jazwa/rackstack/media/features/slideOpt.gif

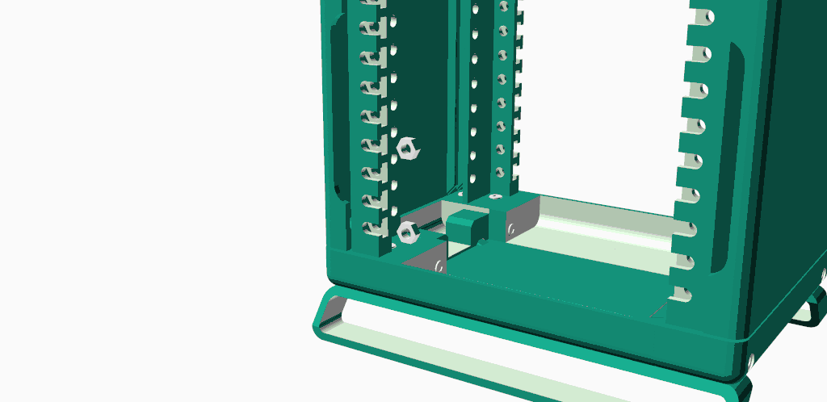
media/features/slideOpt.gif
