jazwa/rackstack/media/features/stackConnectorOpt.gif

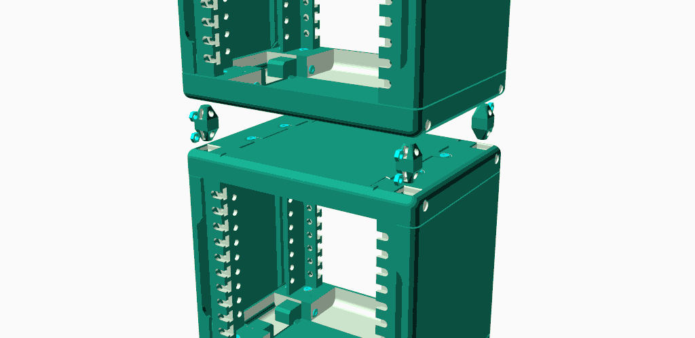
media/features/stackConnectorOpt.gif
