jazwa/rackstack/media/features/swivelOpt.gif

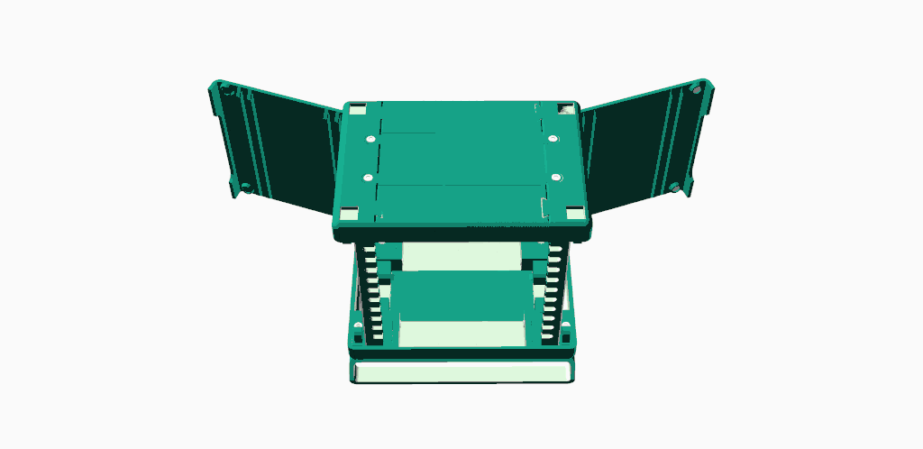
media/features/swivelOpt.gif
