jazwa/rackstack/rack-mount/catalog/120mm-fan-tray_mod.png

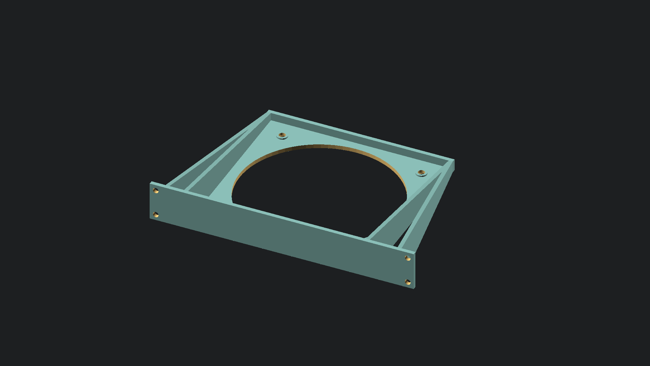
rack-mount/catalog/120mm-fan-tray_mod.png
