jazwa/rackstack/rack-mount/catalog/120mm-Rear-Case-Fan.png

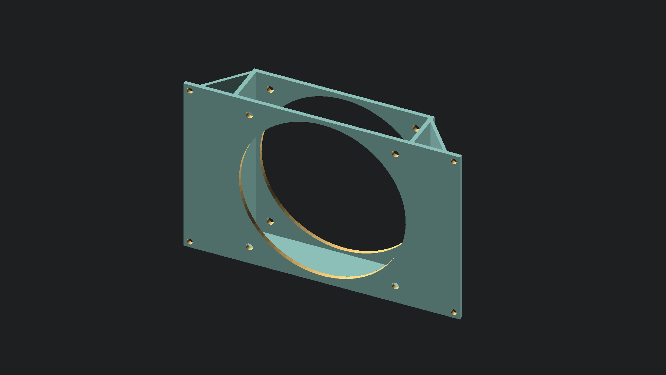
rack-mount/catalog/120mm-Rear-Case-Fan.png
