jazwa/rackstack/rack-mount/catalog/beelink-EQi12-box_mod.png

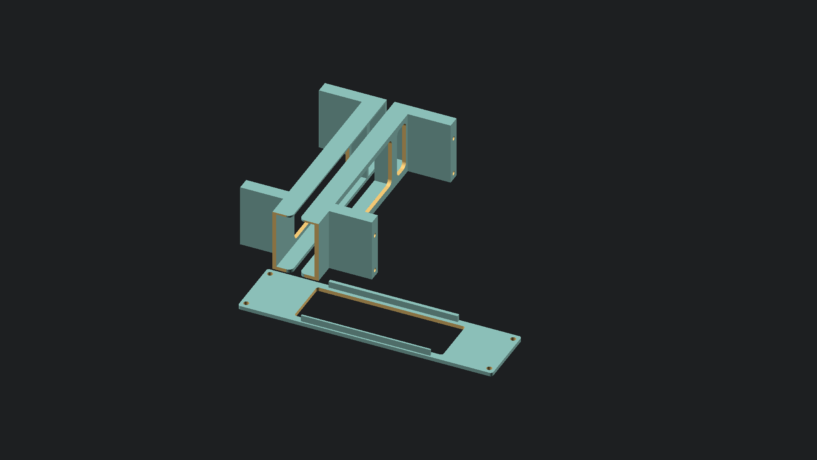
rack-mount/catalog/beelink-EQi12-box_mod.png
