jazwa/rackstack/rack-mount/catalog/beelink-EQi12-tray_mod.png

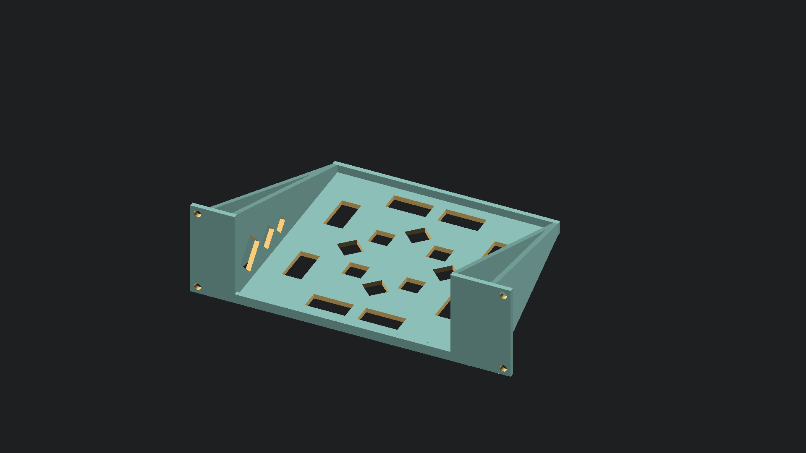
rack-mount/catalog/beelink-EQi12-tray_mod.png
