jazwa/rackstack/rack-mount/catalog/brush-strip-plate.png

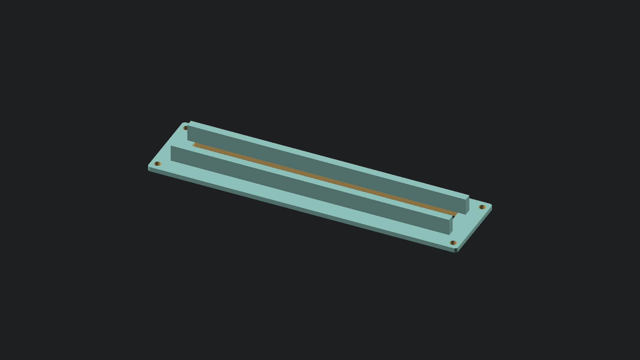
rack-mount/catalog/brush-strip-plate.png
