jazwa/rackstack/rack-mount/catalog/mele-quieter-tray.png

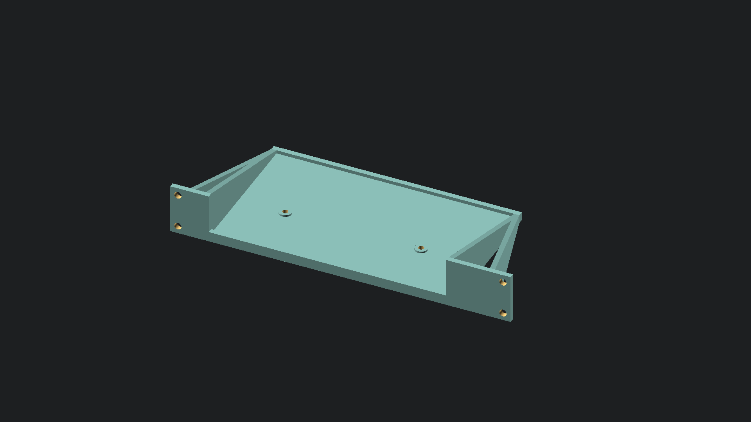
rack-mount/catalog/mele-quieter-tray.png
