jazwa/rackstack/rack-mount/catalog/rpi-sbc-simple-box/case.png

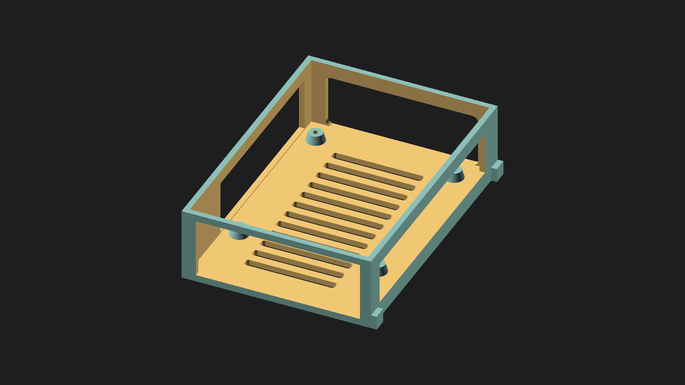
rack-mount/catalog/rpi-sbc-simple-box/case.png
