jazwa/rackstack/rack-mount/catalog/rpi-sbc-simple-box/top.png

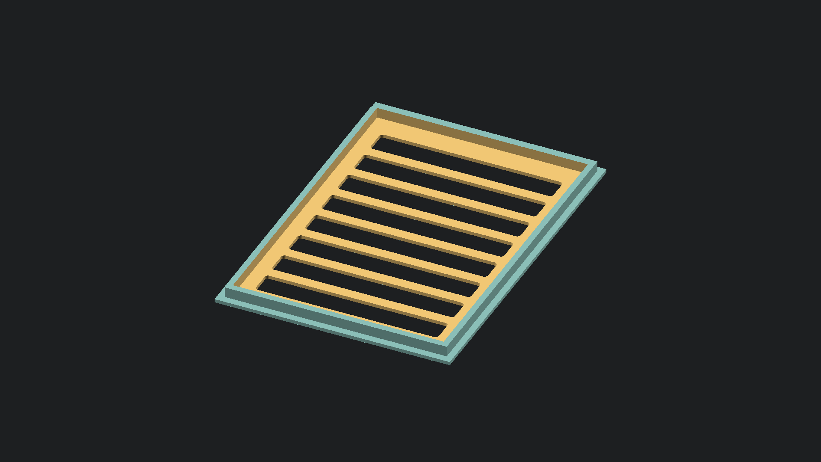
rack-mount/catalog/rpi-sbc-simple-box/top.png
