jazwa/rackstack/rack-mount/catalog/Unifi-8-PoE-Switch_Tray+Adapter.png

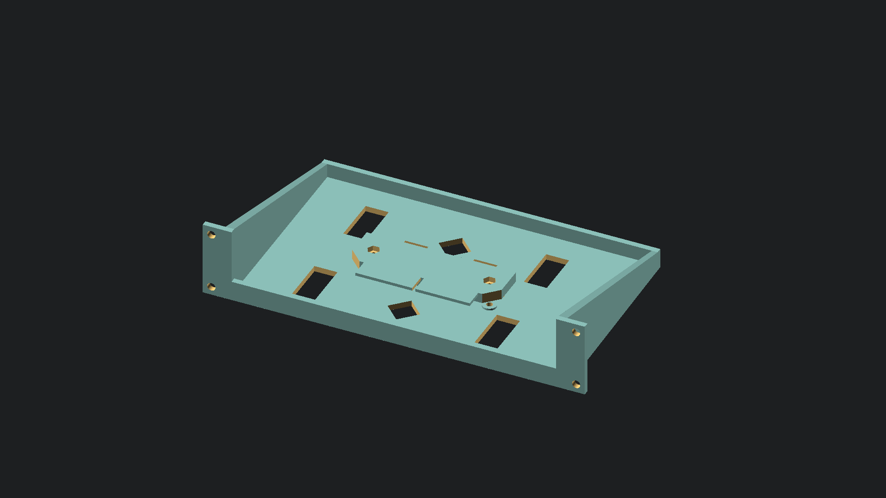
rack-mount/catalog/Unifi-8-PoE-Switch_Tray+Adapter.png
