jazwa/rackstack/power/stl/topBarInsert.stl

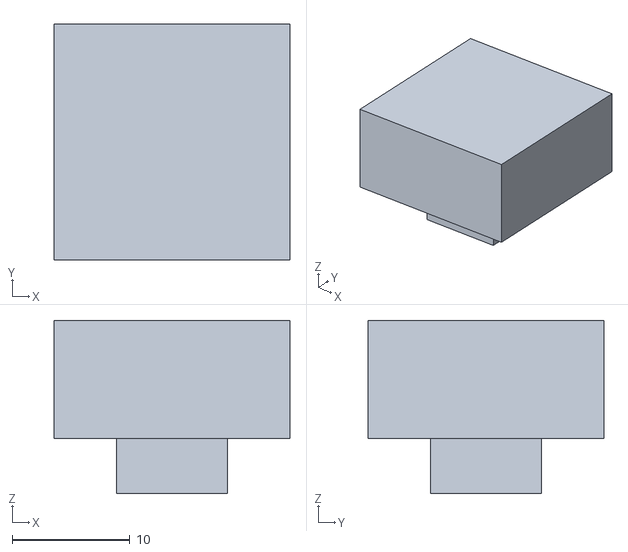
[picture p39: CAD file, 2022-04-04]
power/stl/topBarInsert.stl
20.0 x 20.0 x 14.7
