jazwa/rackstack/rack/rackCaselid.stl

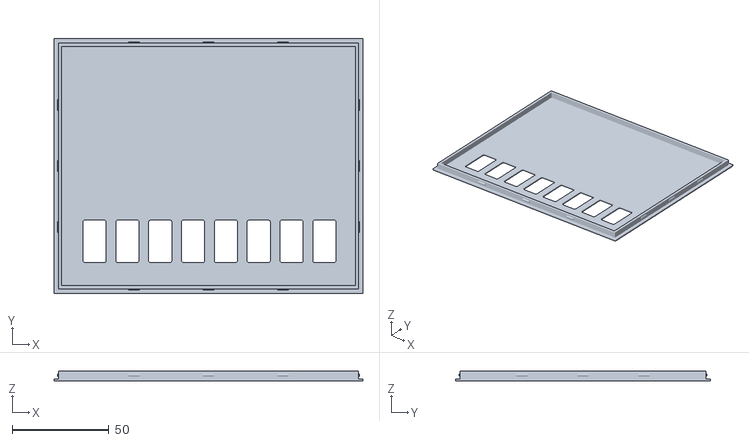
[picture p40: CAD file, 2022-11-05]
rack/rackCaselid.stl
160.0 x 132.0 x 5.00
