jazwa/rackstack/stl/micro/rack/rackFeet_P.stl

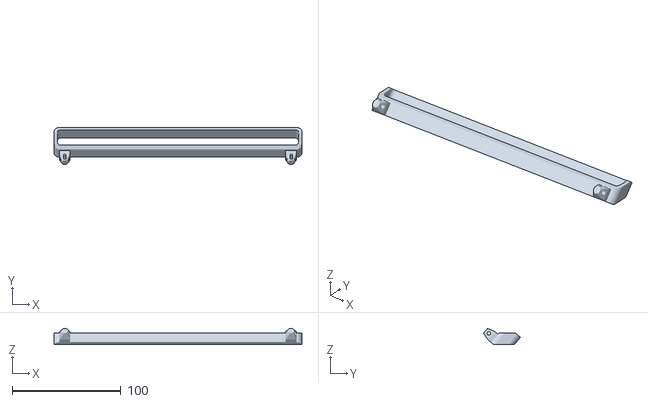
[picture p41: CAD file, 2024-10-19]
stl/micro/rack/rackFeet_P.stl
228.0 x 34.0 x 15.0
