jazwa/rackstack/stl/mini/rack/xBar_P.stl

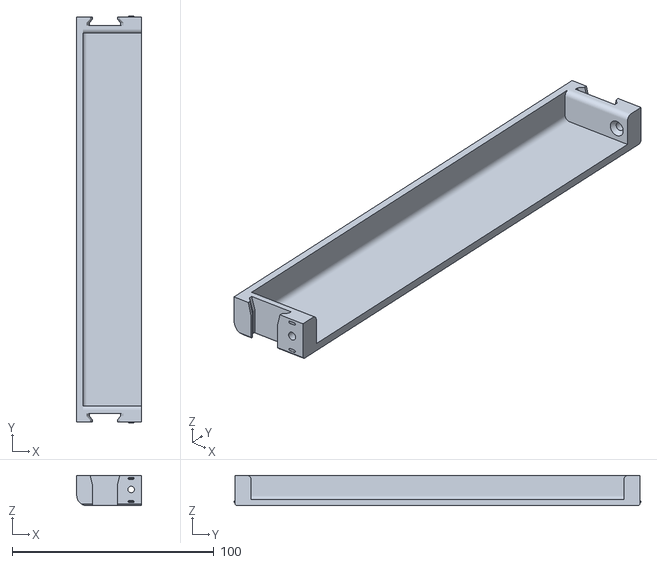
[picture p42: CAD file, 2024-10-19]
stl/mini/rack/xBar_P.stl
32.0 x 201.8 x 15.0
