jazwa/rackstack/stl/nano/rack/rackJoiner_P.stl

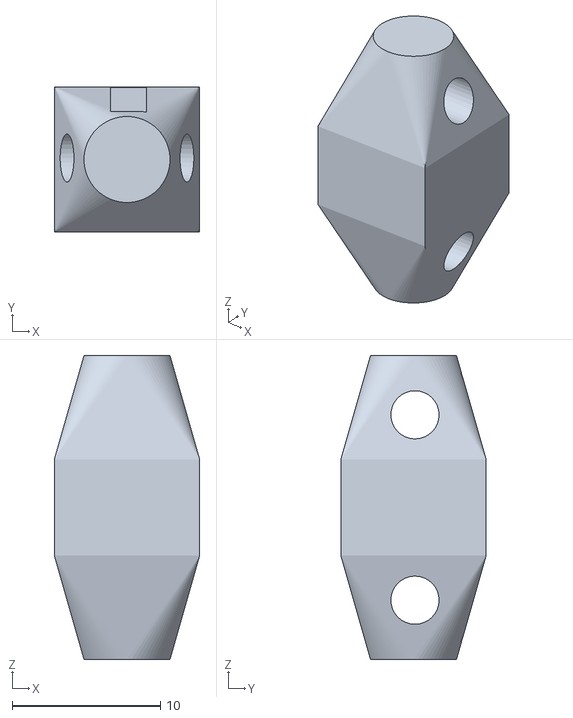
[picture p43: CAD file, 2024-10-19]
stl/nano/rack/rackJoiner_P.stl
9.80 x 9.80 x 20.5
