jazwa/rackstack/power/stl/plate.stl

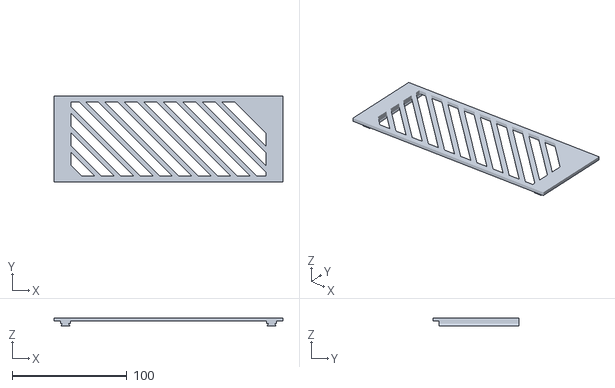
[picture p44: CAD file, 2022-04-04]
power/stl/plate.stl
200.0 x 75.0 x 7.33
