jazwa/rackstack/stl/micro/rack/magnetModuleRight_P.stl

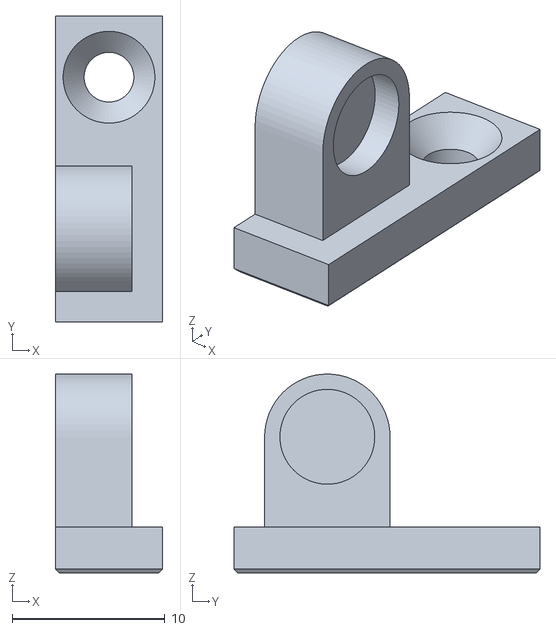
[picture p45: CAD file, 2024-10-19]
stl/micro/rack/magnetModuleRight_P.stl
7.00 x 20.0 x 13.0
