jazwa/rackstack/stl/mini/rack/sideWallLeft_P.stl

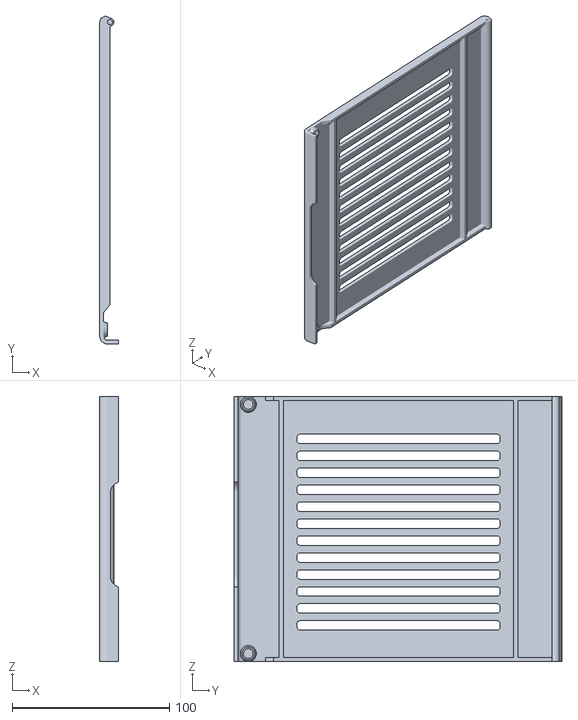
[picture p46: CAD file, 2024-10-19]
stl/mini/rack/sideWallLeft_P.stl
11.8 x 208.3 x 168.4
