jazwa/rackstack/rack/rackCaseForBoxM.stl

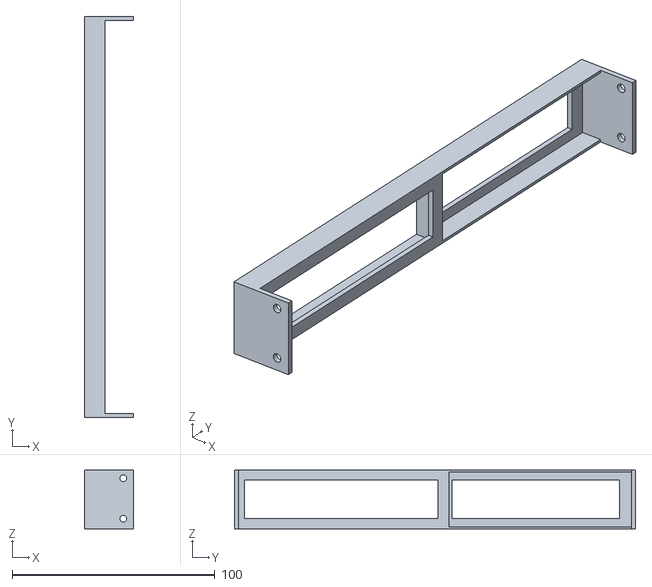
[picture p47: CAD file, 2022-09-18]
rack/rackCaseForBoxM.stl
24.2 x 198.0 x 29.0
