jazwa/rackstack/power/stl/top.stl

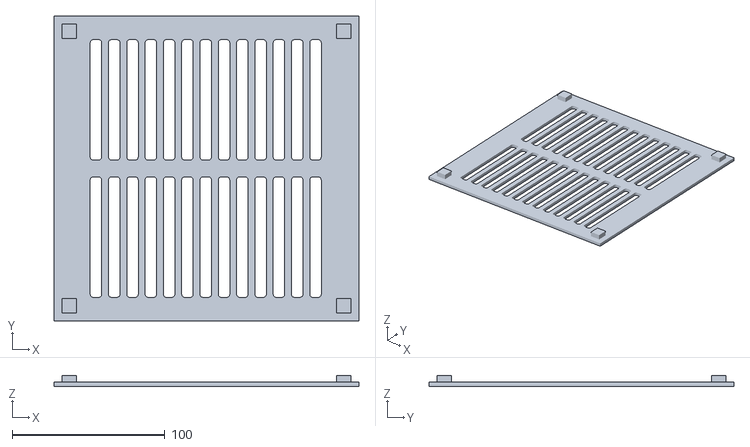
[picture p48: CAD file, 2022-04-04]
power/stl/top.stl
200.0 x 200.0 x 7.50
