jazwa/rackstack/rack/rackCase180.stl

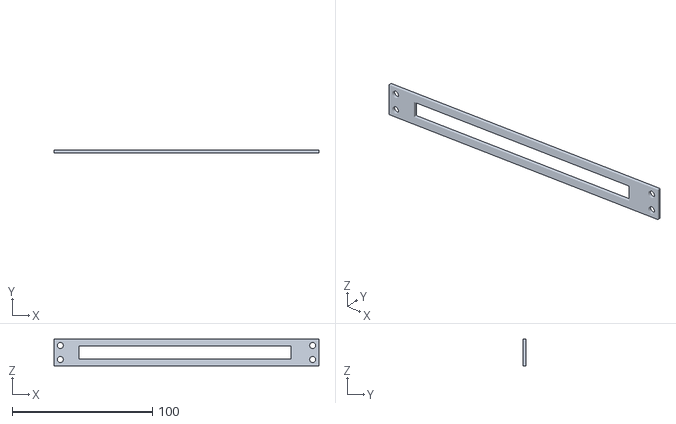
[picture p49: CAD file, 2022-09-18]
rack/rackCase180.stl
189.0 x 2.00 x 19.0
