jazwa/rackstack/stl/micro/rack/yBarLeft_P.stl

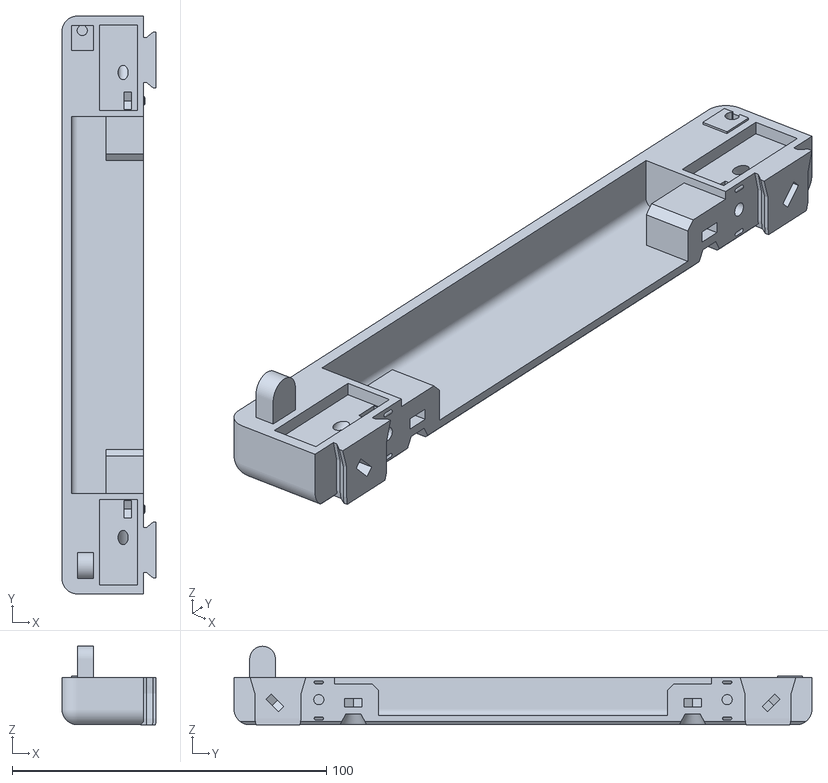
[picture p50: CAD file, 2024-10-19]
stl/micro/rack/yBarLeft_P.stl
30.0 x 184.0 x 25.0
