jazwa/rackstack/power/stl/backPlate.stl

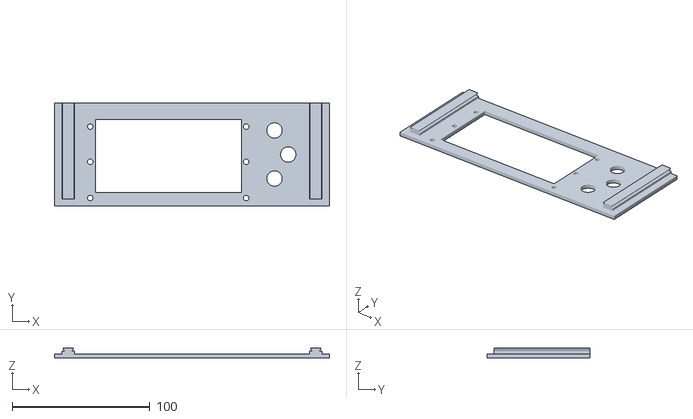
[picture p51: CAD file, 2022-04-04]
power/stl/backPlate.stl
200.0 x 75.0 x 7.32
