jazwa/rackstack/rack/rackCaseForBox.stl

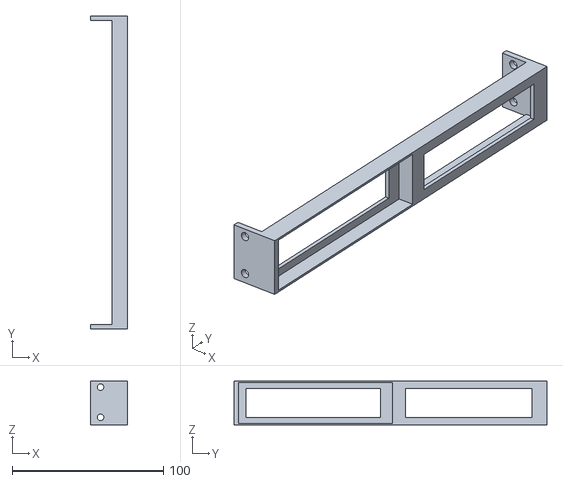
[picture p52: CAD file, 2022-09-18]
rack/rackCaseForBox.stl
24.2 x 207.0 x 29.0
