jazwa/rackstack/power/stl/joinTest.stl

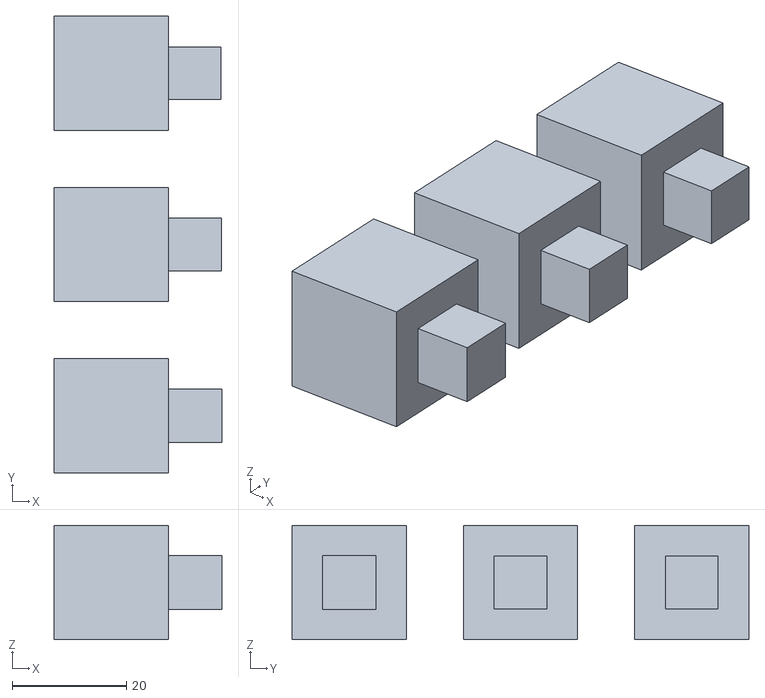
[picture p53: CAD file, 2022-04-04]
power/stl/joinTest.stl
29.4 x 80.0 x 20.0
