jazwa/rackstack/rack/m4LegM.stl

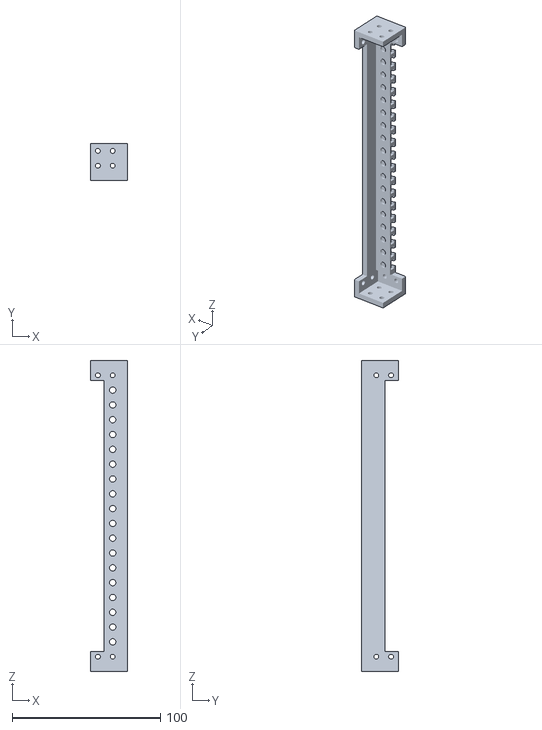
[picture p54: CAD file, 2022-09-18]
rack/m4LegM.stl
25.0 x 25.0 x 210.0
