jazwa/rackstack/stl/mini/rack/yBarLeft_P.stl

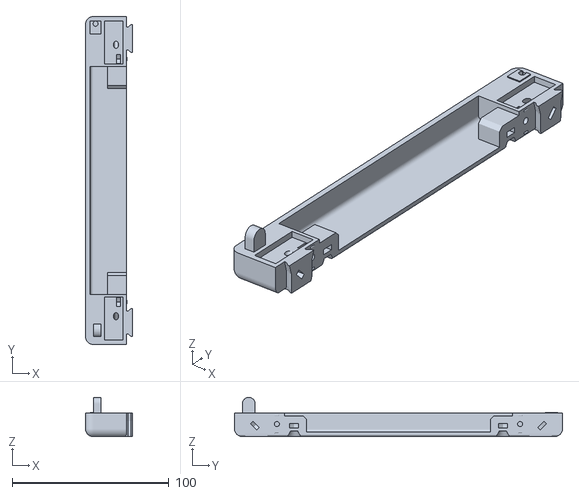
[picture p55: CAD file, 2024-10-19]
stl/mini/rack/yBarLeft_P.stl
30.0 x 209.0 x 25.0
