jazwa/rackstack/stl/nano/rack/xyPlate_P.stl

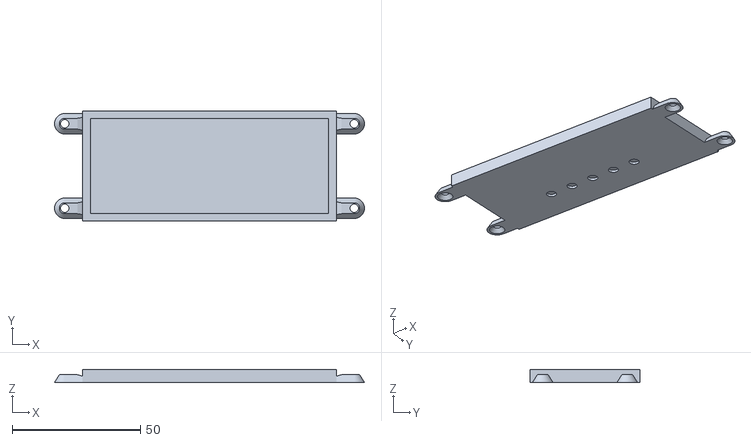
[picture p56: CAD file, 2024-10-19]
stl/nano/rack/xyPlate_P.stl
121.0 x 43.0 x 5.00
