jazwa/rackstack/power/stl/feet.stl

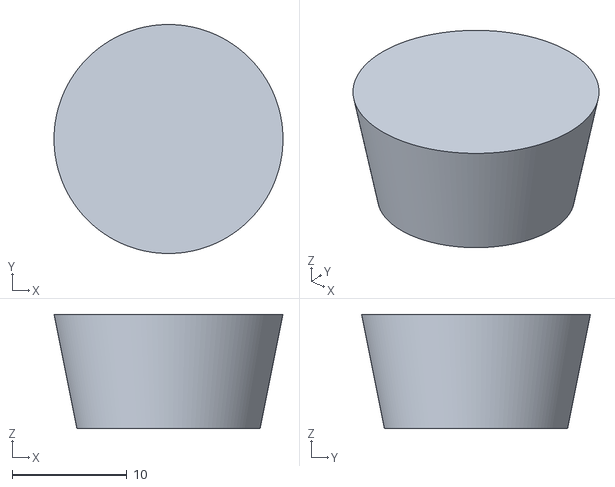
[picture p57: CAD file, 2022-04-04]
power/stl/feet.stl
20.0 x 20.0 x 10.0
