jazwa/rackstack/rack/base1.stl

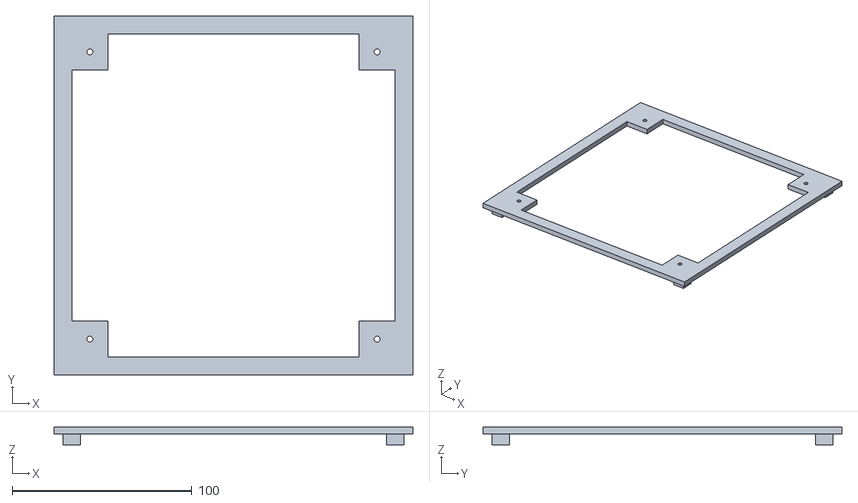
[picture p58: CAD file, 2022-09-18]
rack/base1.stl
200.0 x 200.0 x 10.0
