jazwa/rackstack/stl/micro/rack/xBar_P.stl

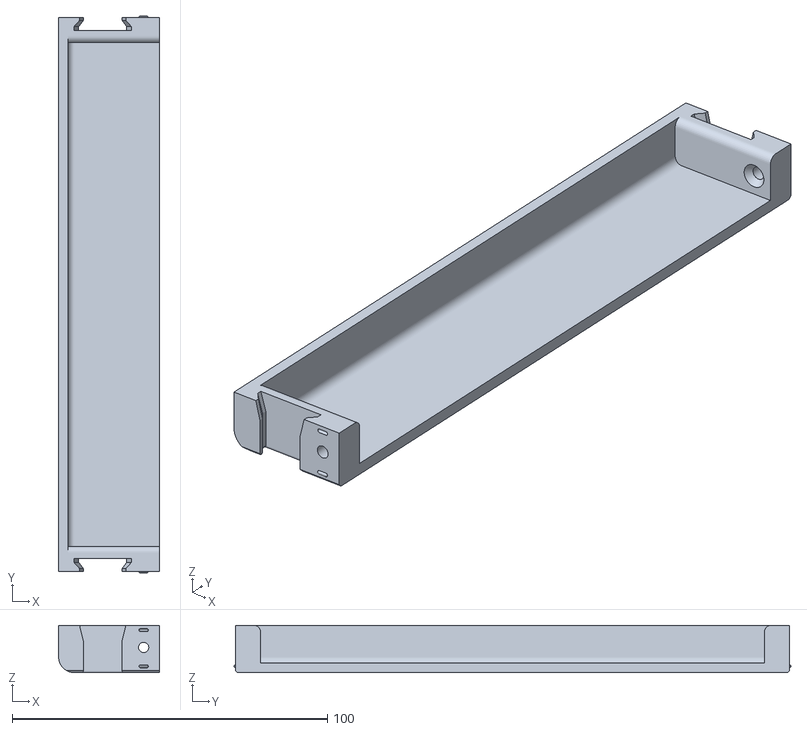
[picture p59: CAD file, 2024-10-19]
stl/micro/rack/xBar_P.stl
32.0 x 176.8 x 15.0
