jazwa/rackstack/stl/nano/rack/sideWallLeft_P.stl

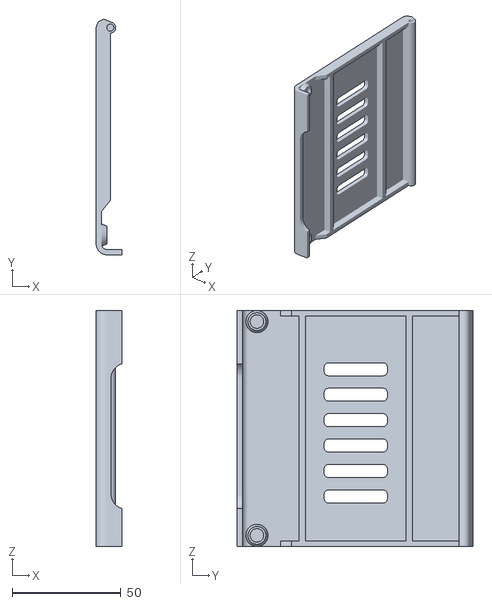
[picture p60: CAD file, 2024-10-19]
stl/nano/rack/sideWallLeft_P.stl
11.8 x 108.3 x 108.4
