jazwa/rackstack/power/stl/support2.stl

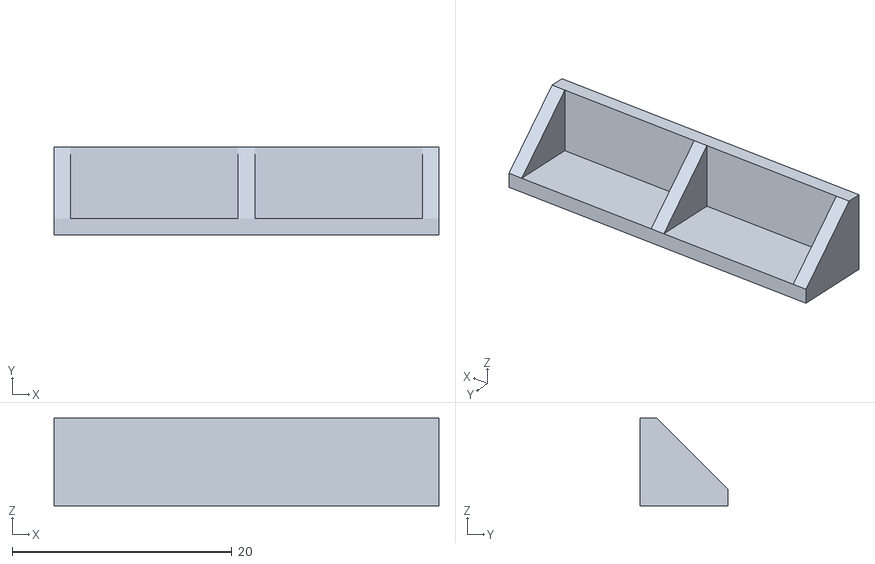
[picture p61: CAD file, 2022-04-04]
power/stl/support2.stl
35.0 x 8.00 x 8.00
