jazwa/rackstack/rack/frontPlate2u.stl

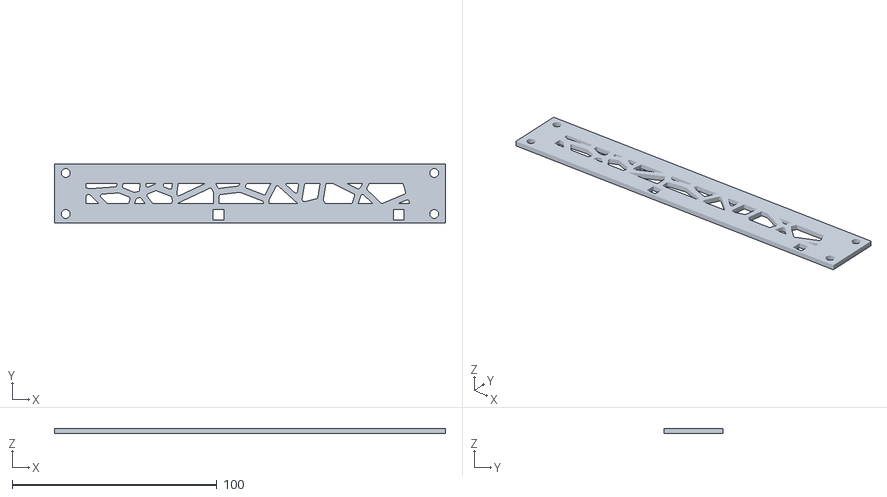
[picture p62: CAD file, 2022-09-18]
rack/frontPlate2u.stl
191.0 x 29.0 x 2.50
