jazwa/rackstack/stl/micro/rack/sideWallRight_P.stl

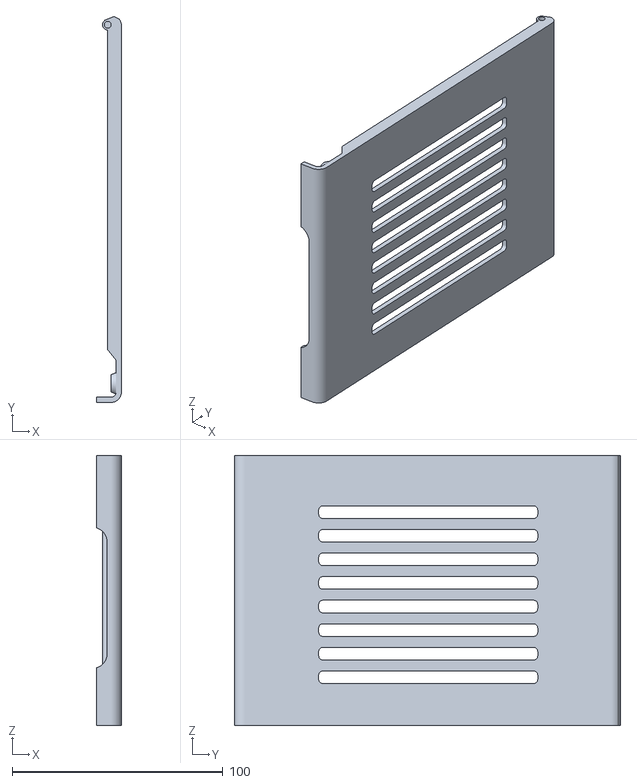
[picture p63: CAD file, 2024-10-19]
stl/micro/rack/sideWallRight_P.stl
11.8 x 183.3 x 128.4
