jazwa/rackstack/stl/mini/rack/rackFeet_P.stl

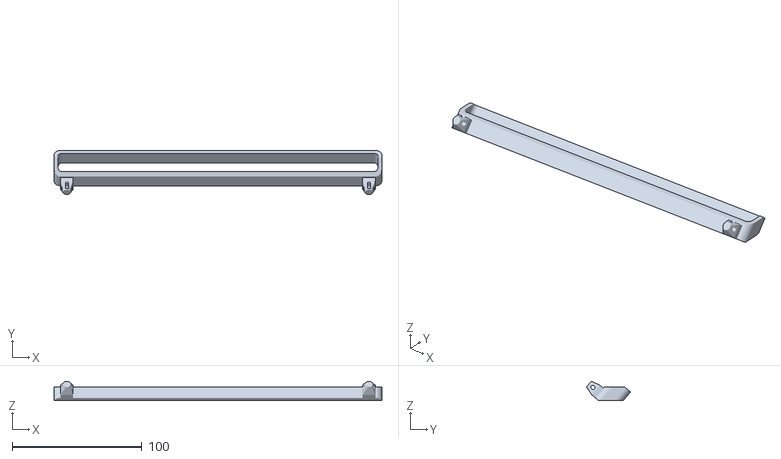
[picture p64: CAD file, 2024-10-19]
stl/mini/rack/rackFeet_P.stl
253.0 x 34.0 x 15.0
