jazwa/rackstack/stl/nano/rack/xBar_P.stl

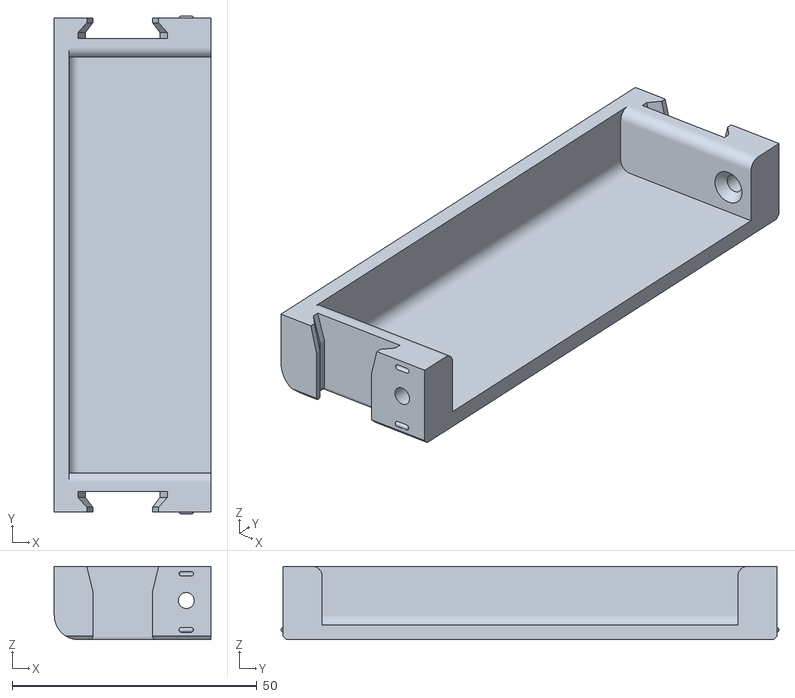
[picture p65: CAD file, 2024-10-19]
stl/nano/rack/xBar_P.stl
32.0 x 101.8 x 15.0
