jazwa/rackstack/power/stl/legTest.stl

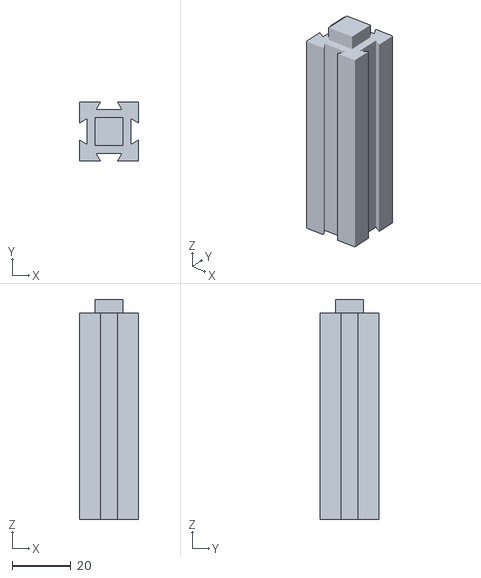
[picture p66: CAD file, 2022-03-14]
power/stl/legTest.stl
20.0 x 20.0 x 74.6
