jazwa/rackstack/stl/mini/rack/xyPlate_P.stl

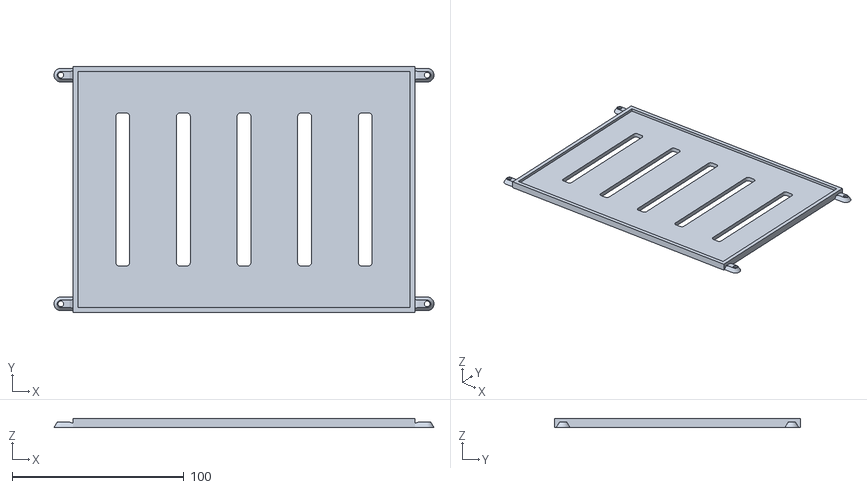
[picture p67: CAD file, 2024-10-19]
stl/mini/rack/xyPlate_P.stl
221.0 x 143.0 x 5.00
