jazwa/rackstack/stl/nano/rack/rackFeet_P.stl

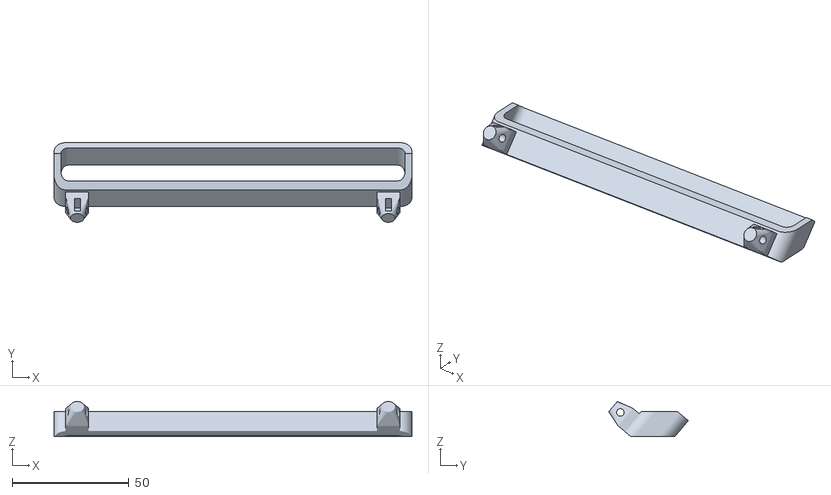
[picture p68: CAD file, 2024-10-19]
stl/nano/rack/rackFeet_P.stl
153.0 x 34.0 x 15.0
