jazwa/rackstack/stl/micro/rack/xyPlate_P.stl

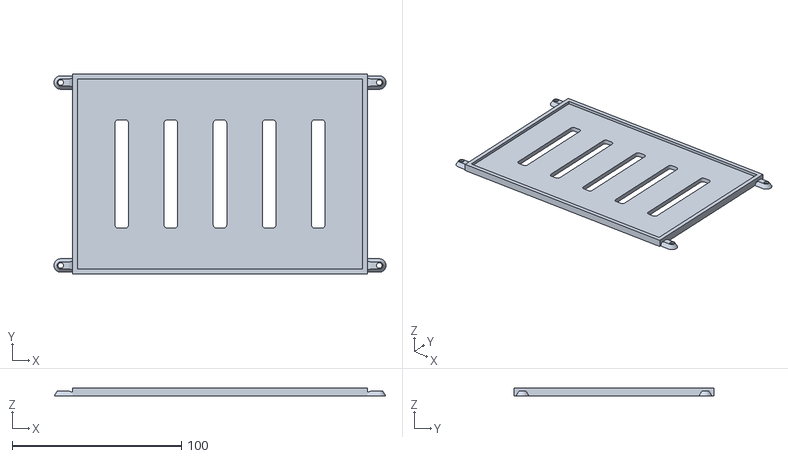
[picture p69: CAD file, 2024-10-19]
stl/micro/rack/xyPlate_P.stl
196.0 x 118.0 x 5.00
