jazwa/rackstack/rack/l1.stl

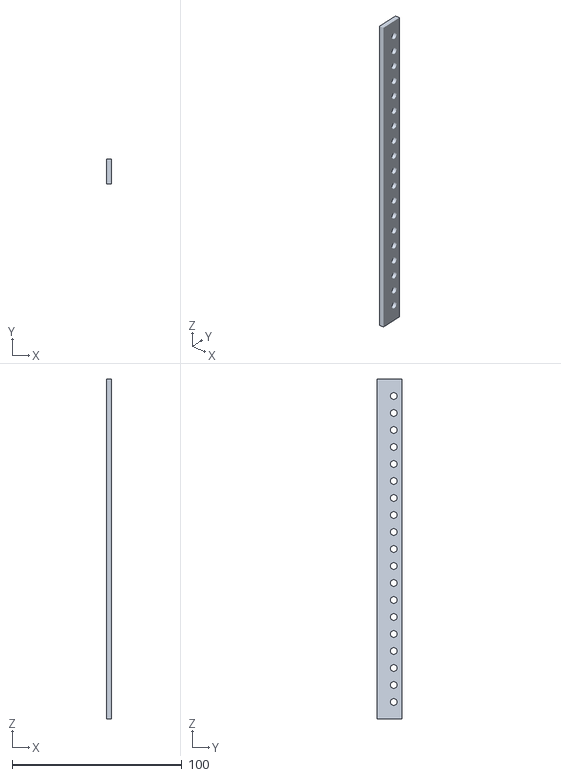
[picture p70: CAD file, 2022-05-29]
rack/l1.stl
3.00 x 15.0 x 200.0
