jazwa/rackstack/rack/legToleranceTest.stl

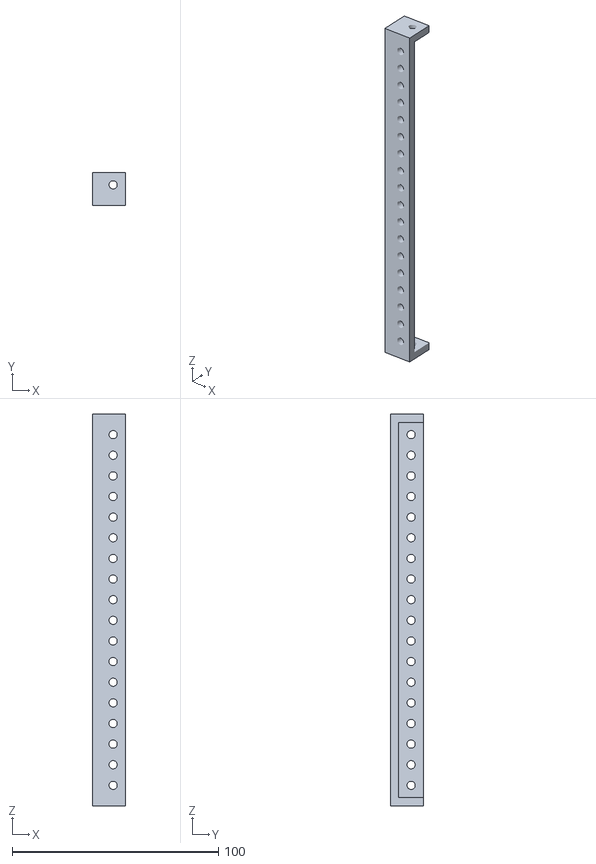
[picture p71: CAD file, 2022-05-29]
rack/legToleranceTest.stl
16.0 x 16.0 x 190.0
