jazwa/rackstack/stl/micro/rack/yBar_P.stl

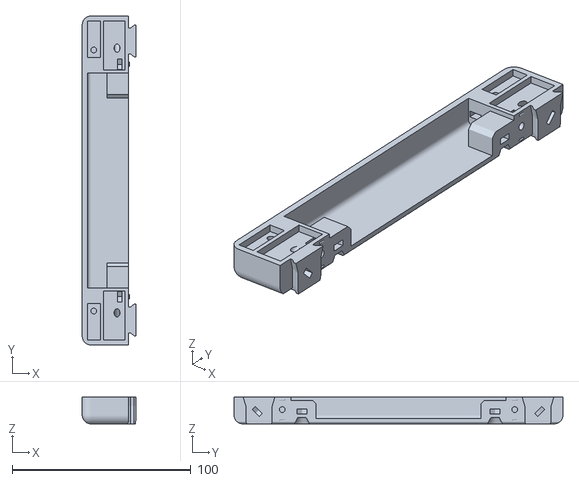
[picture p72: CAD file, 2024-02-25]
stl/micro/rack/yBar_P.stl
30.0 x 184.0 x 15.0
