jazwa/rackstack/stl/mini/rack/yBar_P.stl

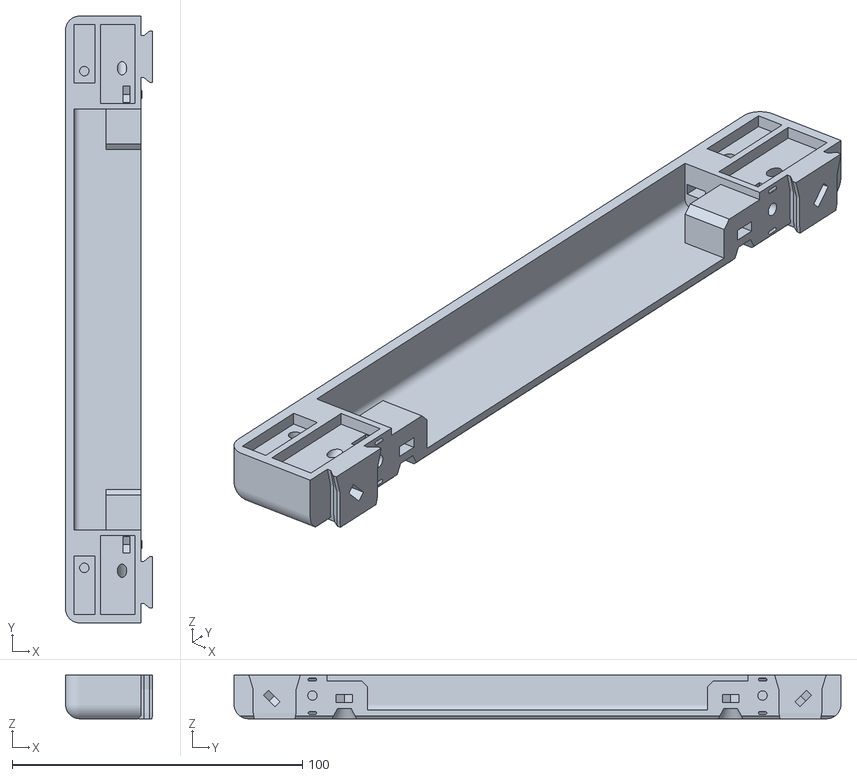
[picture p73: CAD file, 2024-02-25]
stl/mini/rack/yBar_P.stl
30.0 x 209.0 x 15.0
