jazwa/rackstack/stl/nano/rack/yBar_P.stl

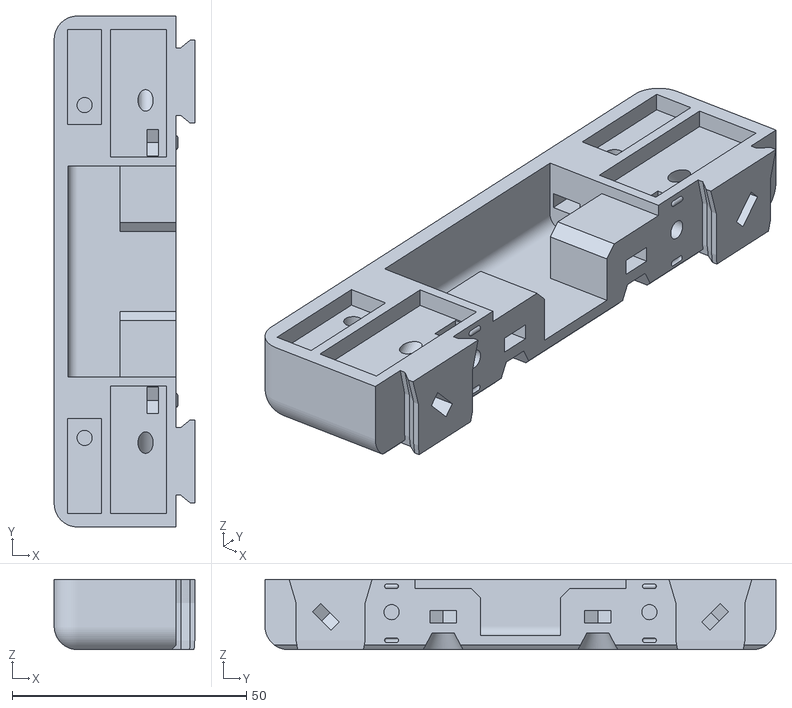
[picture p74: CAD file, 2024-02-25]
stl/nano/rack/yBar_P.stl
30.0 x 109.0 x 15.0
