jazwa/rackstack/config/common.scad

// Config aggregator file + some extra configs
include <./dowel.scad>
include <./magnet.scad>
include <./rackFrame.scad>
include <./print.scad>


sideWallVentilation = true;
