jazwa/rackstack/config/dowel.scad

/*
  Dowel pin config used in side wall hinge module and side wall
*/

dowelPinR = 1.5;
dowelPinH = 10;
