jazwa/rackstack/helper/common.scad

// Helper aggregator

include <./apply.scad>
include <./dovetail.scad>
include <./filet.scad>
include <./keystone1.scad>
include <./keystone2.scad>
include <./math.scad>
include <./matrix.scad>
include <./screws.scad>
include <./sine.scad>

$fn=64;
