jazwa/rackstack/assembly-guide/gifs/attachSideConnectorModulesToYBars.gif

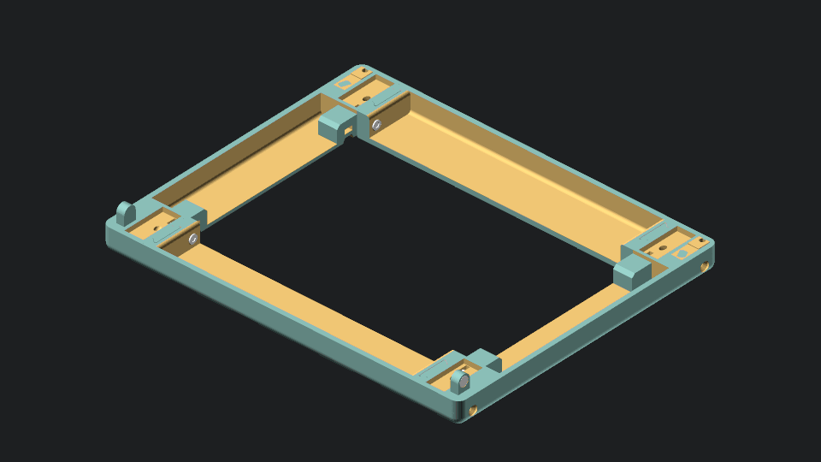
assembly-guide/gifs/attachSideConnectorModulesToYBars.gif
